jimrains/OpenRIS/hardware/gerber/openris_stackup_v1p0.png

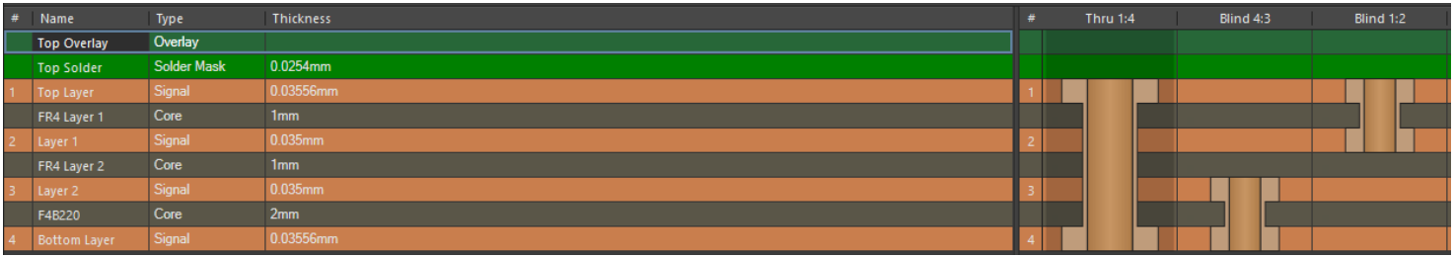
hardware/gerber/openris_stackup_v1p0.png
