jimrains/OpenRIS/measurements/ff_singletile/tx_105_VV/rx_0/11.csv

!CSV A.01.01
!Keysight Technologies | N5247A | US56070710 | A.10.64.09
!Date: Saturday | November 19 | 2022 23:56:28
!Source: Standard
BEGIN CH1_DATA
Freq(Hz) | S33(DB) | S33(DEG) | S34(DB) | S34(DEG) | S43(DB) | S43(DEG) | S44(DB) | S44(DEG)
3000000000 | -10.265381 | 173.06259 | -63.508152 | -97.622971 | -63.220905 | -98.302368 | -18.28961 | -162.02106
3005000000 | -16.208401 | 65.150307 | -63.032806 | 178.15498 | -63.161469 | 179.80299 | -17.340364 | -156.11528
3010000000 | -10.727672 | 106.82088 | -61.040588 | 88.111664 | -61.007317 | 94.251816 | -15.619514 | -169.05171
3015000000 | -9.4030037 | 168.05885 | -59.74575 | 14.924283 | -59.631153 | 13.062865 | -15.893877 | -156.78915
3020000000 | -13.553293 | 28.085167 | -58.948036 | -78.999474 | -58.857697 | -78.933929 | -16.543102 | -176.78864
3025000000 | -6.5056887 | 131.06459 | -58.516914 | -156.40802 | -58.504982 | -161.72382 | -14.661705 | -162.87543
3030000000 | -26.261974 | 161.71719 | -58.689396 | 103.68584 | -58.411766 | 103.20876 | -18.689196 | 177.46962
3035000000 | -11.35969 | 59.265457 | -57.912724 | 10.722267 | -58.266586 | 10.686119 | -14.073341 | -173.99721
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
