jimrains/OpenRIS/measurements/ff_singletile/tx_105_VV/rx_0/2.csv

!CSV A.01.01
!Keysight Technologies | N5247A | US56070710 | A.10.64.09
!Date: Saturday | November 19 | 2022 23:55:46
!Source: Standard
BEGIN CH1_DATA
Freq(Hz) | S33(DB) | S33(DEG) | S34(DB) | S34(DEG) | S43(DB) | S43(DEG) | S44(DB) | S44(DEG)
3000000000 | -10.229579 | 174.00266 | -64.099052 | -100.26659 | -63.232944 | -103.41891 | -18.255997 | -165.77719
3005000000 | -15.153021 | 64.209641 | -63.410374 | 172.94206 | -62.871243 | 173.15967 | -17.470869 | -159.23422
3010000000 | -10.873618 | 103.25822 | -60.756123 | 86.524971 | -60.973858 | 85.819298 | -15.486868 | -172.63376
3015000000 | -9.1529884 | 166.37198 | -59.855343 | 7.3538256 | -59.94516 | 9.8640394 | -15.981023 | -159.15955
3020000000 | -12.635807 | 25.119366 | -58.773312 | -85.009026 | -58.619144 | -82.45742 | -16.449245 | 179.44345
3025000000 | -6.3877082 | 130.4037 | -59.067032 | -164.76178 | -58.997723 | -164.19717 | -14.698215 | -165.25317
3030000000 | -27.6075 | 144.72731 | -58.942116 | 101.55383 | -58.947979 | 101.49078 | -18.625734 | 173.22272
3035000000 | -11.129218 | 55.007259 | -58.370228 | 10.433052 | -58.559422 | 9.6759872 | -14.149739 | -176.60094
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
