jimrains/OpenRIS/measurements/ff_singletile/tx_105_VV/rx_0/3.csv

!CSV A.01.01
!Keysight Technologies | N5247A | US56070710 | A.10.64.09
!Date: Saturday | November 19 | 2022 23:55:50
!Source: Standard
BEGIN CH1_DATA
Freq(Hz) | S33(DB) | S33(DEG) | S34(DB) | S34(DEG) | S43(DB) | S43(DEG) | S44(DB) | S44(DEG)
3000000000 | -10.243275 | 173.86096 | -63.05418 | -100.86771 | -63.268772 | -98.634445 | -18.250832 | -165.89458
3005000000 | -15.235882 | 64.446838 | -63.446136 | 176.30037 | -62.976025 | 177.60321 | -17.495388 | -159.1566
3010000000 | -10.878606 | 103.46442 | -60.606457 | 87.676765 | -60.694828 | 87.887703 | -15.481614 | -172.36665
3015000000 | -9.1731949 | 166.40071 | -59.237358 | 8.2922745 | -60.207924 | 7.1733661 | -15.956948 | -159.27853
3020000000 | -12.719115 | 25.299385 | -58.968594 | -81.952637 | -58.64233 | -84.65992 | -16.472155 | 179.40277
3025000000 | -6.4072571 | 130.42195 | -58.746159 | -163.18359 | -59.030724 | -161.7213 | -14.704115 | -165.06096
3030000000 | -27.418758 | 145.6835 | -58.672859 | 99.808464 | -58.901669 | 101.82793 | -18.594824 | 173.47424
3035000000 | -11.165936 | 55.284817 | -58.421188 | 8.6879492 | -57.776897 | 7.4661207 | -14.14166 | -176.72754
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
