jimrains/OpenRIS/measurements/ff_singletile/tx_105_VV/rx_0/4.csv

!CSV A.01.01
!Keysight Technologies | N5247A | US56070710 | A.10.64.09
!Date: Saturday | November 19 | 2022 23:55:55
!Source: Standard
BEGIN CH1_DATA
Freq(Hz) | S33(DB) | S33(DEG) | S34(DB) | S34(DEG) | S43(DB) | S43(DEG) | S44(DB) | S44(DEG)
3000000000 | -10.243326 | 173.75266 | -63.391911 | -101.09532 | -63.207886 | -99.305351 | -18.260902 | -165.5202
3005000000 | -15.331752 | 64.308372 | -63.346642 | 172.56973 | -62.695278 | 176.56314 | -17.456514 | -159.12419
3010000000 | -10.842067 | 103.82822 | -60.679218 | 88.413277 | -60.995361 | 89.349205 | -15.495275 | -172.36659
3015000000 | -9.202096 | 166.62657 | -59.746773 | 9.0905228 | -59.549809 | 11.209922 | -15.972497 | -159.13321
3020000000 | -12.787556 | 25.601803 | -58.387619 | -84.341202 | -58.75148 | -81.640854 | -16.464766 | 179.72075
3025000000 | -6.411489 | 130.45279 | -58.681168 | -162.78683 | -59.061073 | -163.74951 | -14.690157 | -165.14279
3030000000 | -27.401905 | 148.19278 | -58.521706 | 101.09496 | -58.589882 | 101.63742 | -18.632 | 173.47827
3035000000 | -11.162694 | 55.684696 | -57.944122 | 10.595945 | -58.253719 | 9.8181524 | -14.139631 | -176.48976
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
